mishacucicea/RedAlert/API/RedAlert.API/RedAlert.API/Content/img/beforecompresing/chooseaction.png

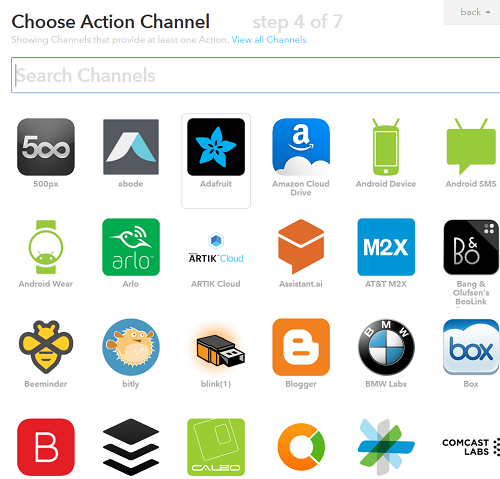
API/RedAlert.API/RedAlert.API/Content/img/beforecompresing/chooseaction.png
