mishacucicea/RedAlert/API/RedAlert.API/RedAlert.API/Content/img/beforecompresing/choosetriggerchanel.PNG

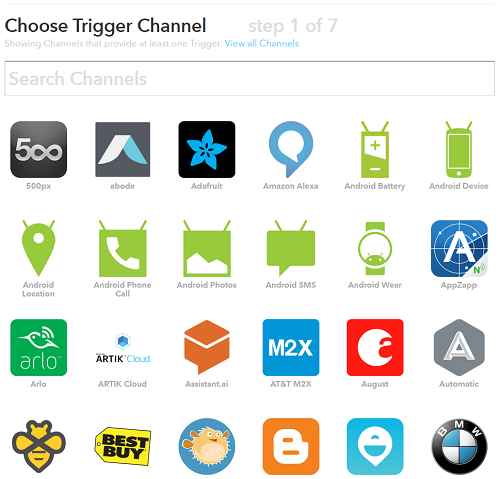
API/RedAlert.API/RedAlert.API/Content/img/beforecompresing/choosetriggerchanel.PNG
