mishacucicea/RedAlert/API/RedAlert.API/RedAlert.API/Content/img/beforecompresing/colorbubble.png

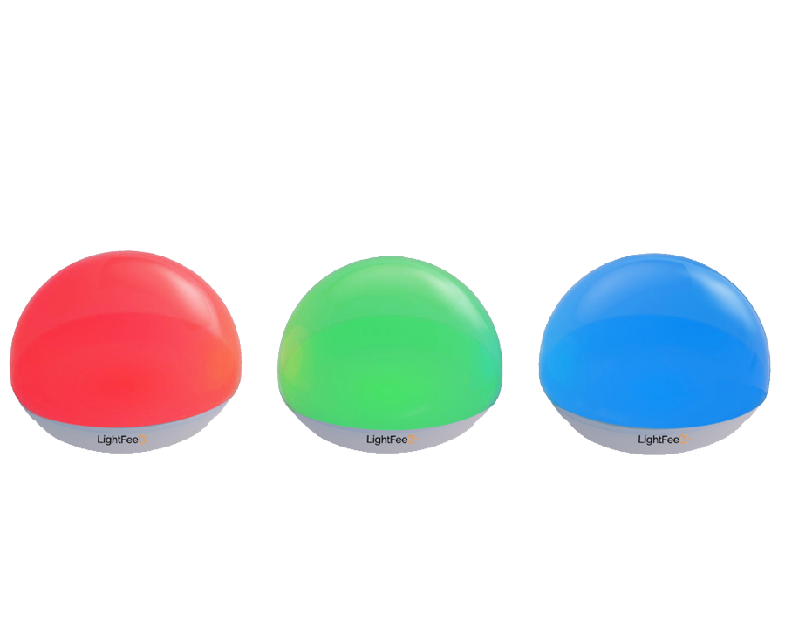
API/RedAlert.API/RedAlert.API/Content/img/beforecompresing/colorbubble.png
