mishacucicea/RedAlert/API/RedAlert.API/RedAlert.API/Content/img/beforecompresing/Colorbubbles.jpg

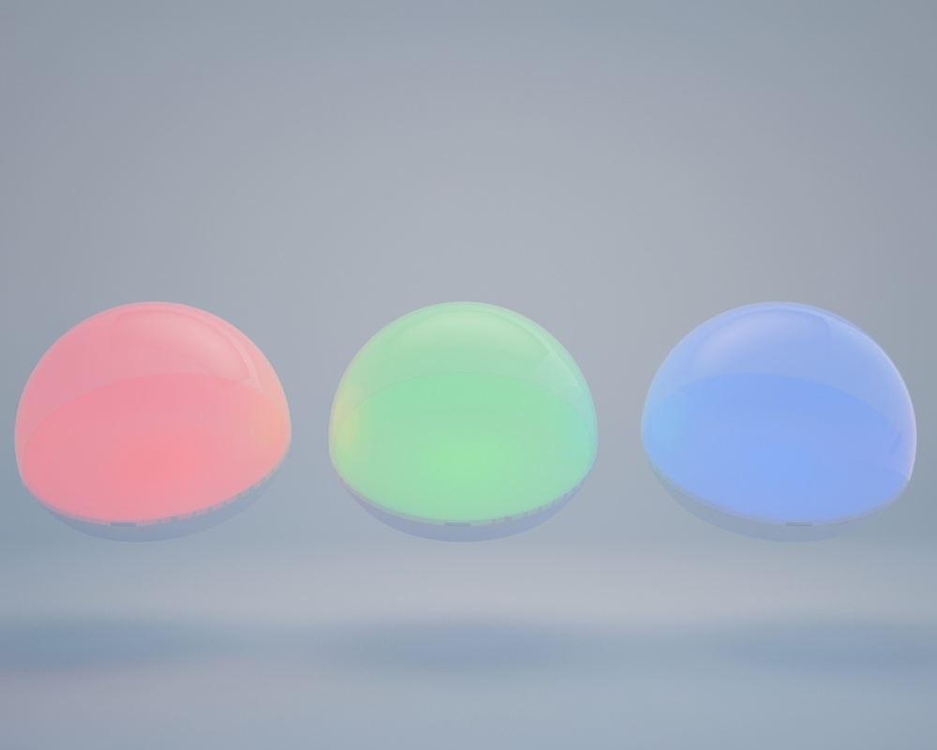
API/RedAlert.API/RedAlert.API/Content/img/beforecompresing/Colorbubbles.jpg
