mishacucicea/RedAlert/API/RedAlert.API/RedAlert.API/Content/img/beforecompresing/devicepsd.jpg

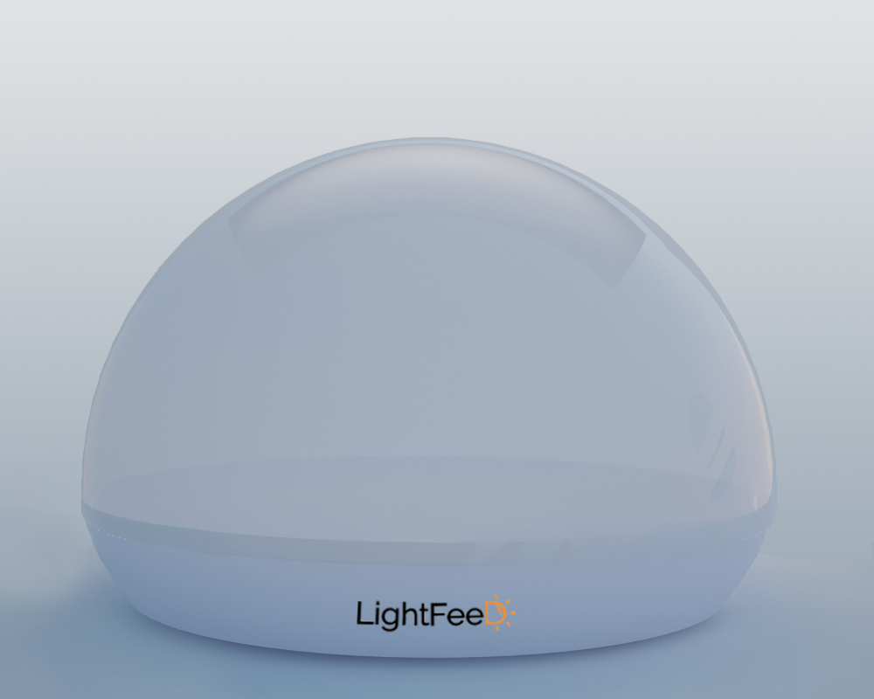
API/RedAlert.API/RedAlert.API/Content/img/beforecompresing/devicepsd.jpg
