mishacucicea/RedAlert/API/RedAlert.API/RedAlert.API/Content/img/beforecompresing/devicepsd.png

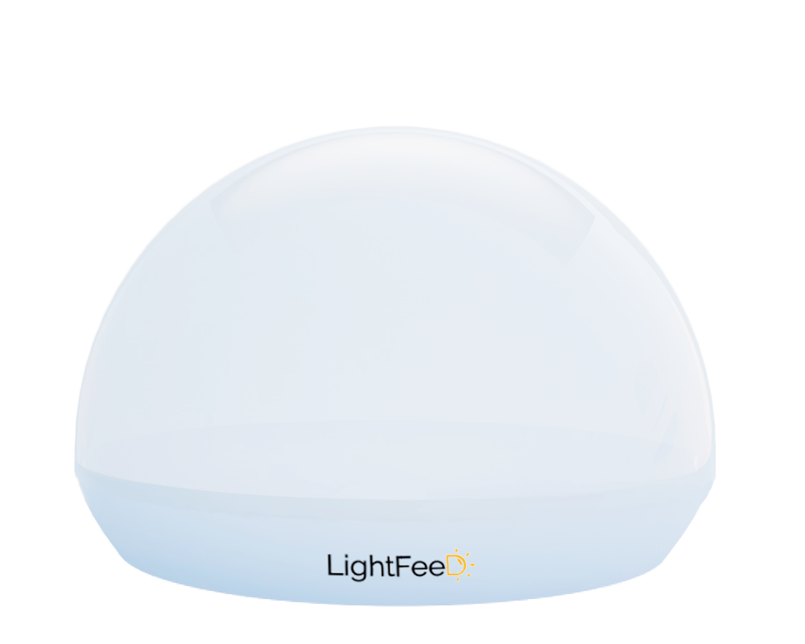
API/RedAlert.API/RedAlert.API/Content/img/beforecompresing/devicepsd.png
