mishacucicea/RedAlert/API/RedAlert.API/RedAlert.API/Content/img/beforecompresing/jenkins-solution.png

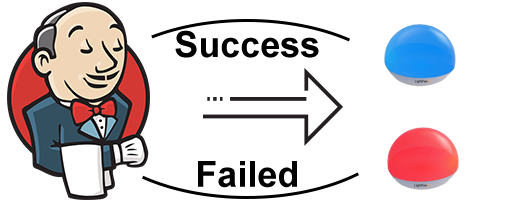
API/RedAlert.API/RedAlert.API/Content/img/beforecompresing/jenkins-solution.png
