mishacucicea/RedAlert/API/RedAlert.API/RedAlert.API/Content/img/beforecompresing/jenkins.jpg

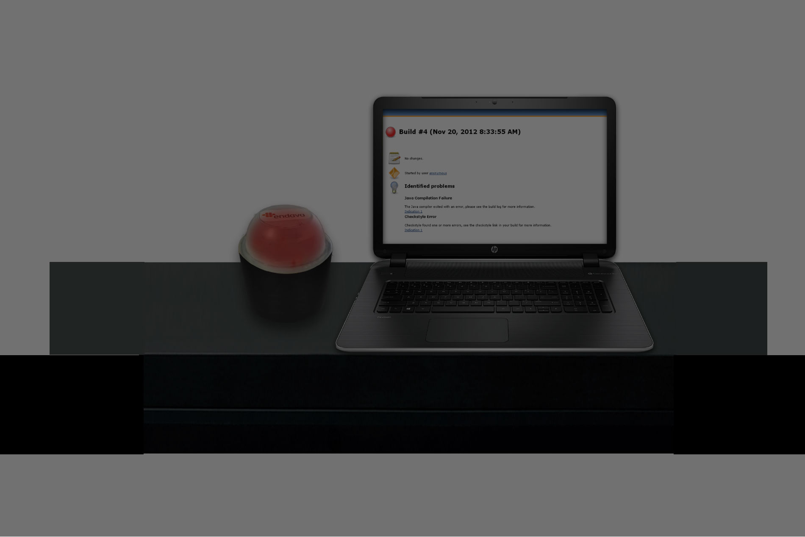
API/RedAlert.API/RedAlert.API/Content/img/beforecompresing/jenkins.jpg
