mishacucicea/RedAlert/API/RedAlert.API/RedAlert.API/Content/img/beforecompresing/scanqr.png

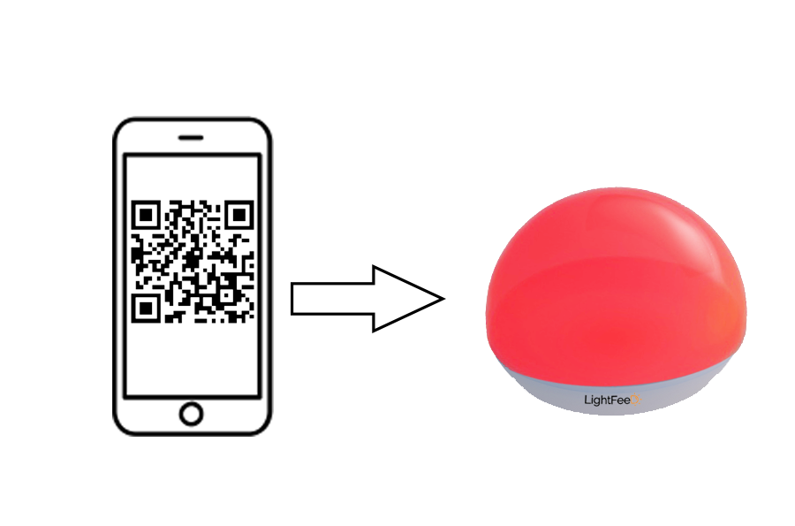
API/RedAlert.API/RedAlert.API/Content/img/beforecompresing/scanqr.png
