mishacucicea/RedAlert/API/RedAlert.API/RedAlert.API/Content/img/devicepsd.png

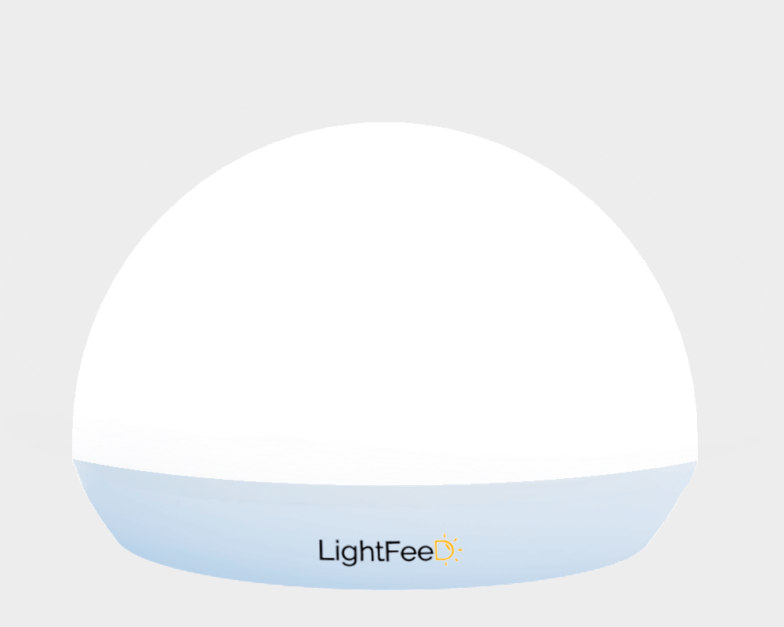
API/RedAlert.API/RedAlert.API/Content/img/devicepsd.png
