mishacucicea/RedAlert/API/RedAlert.API/RedAlert.API/Content/img/devicepsdxx.png

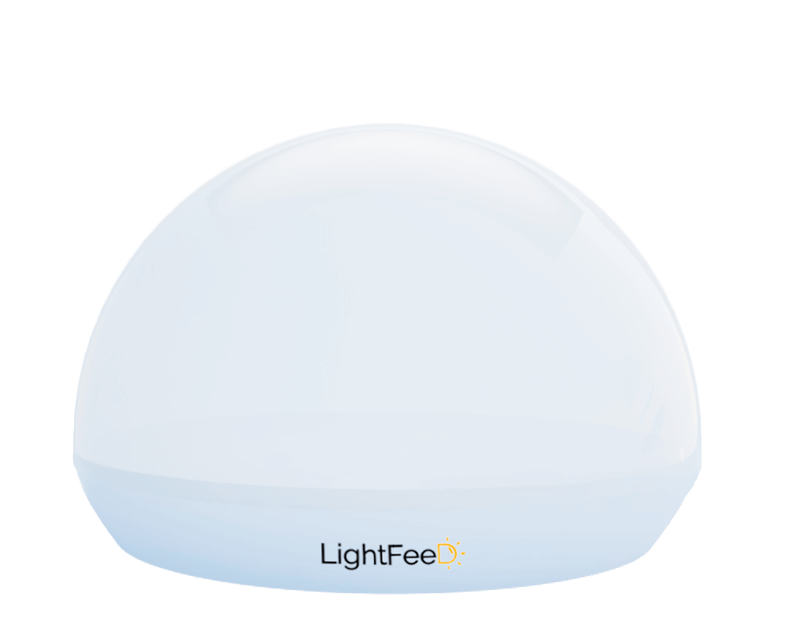
API/RedAlert.API/RedAlert.API/Content/img/devicepsdxx.png
