mishacucicea/RedAlert/API/RedAlert.API/RedAlert.API/Content/img/Frame50.gif

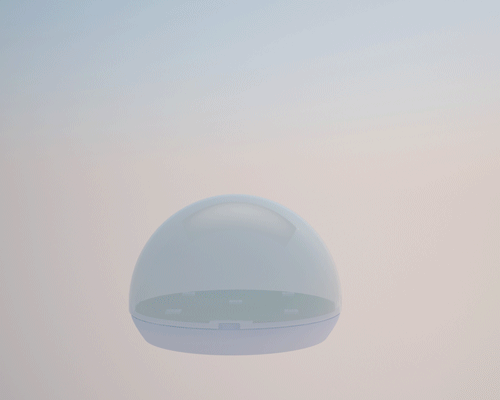
API/RedAlert.API/RedAlert.API/Content/img/Frame50.gif
