mishacucicea/RedAlert/API/RedAlert.API/RedAlert.API/Content/img/iftttlight.png

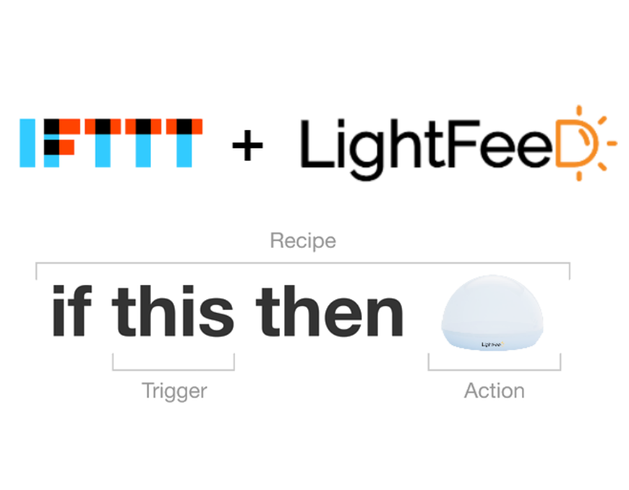
API/RedAlert.API/RedAlert.API/Content/img/iftttlight.png
