mishacucicea/RedAlert/API/RedAlert.API/RedAlert.API/Content/img/RGB_circle.png

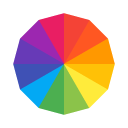
API/RedAlert.API/RedAlert.API/Content/img/RGB_circle.png
