mishacucicea/RedAlert/API/RedAlert.API/RedAlert.API/Content/img/team/1.jpg

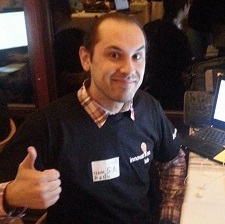
API/RedAlert.API/RedAlert.API/Content/img/team/1.jpg
