mishacucicea/RedAlert/API/RedAlert.API/RedAlert.API/Content/img/team/2.jpg

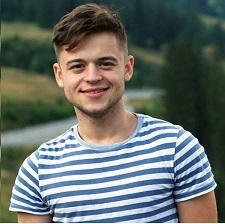
API/RedAlert.API/RedAlert.API/Content/img/team/2.jpg
