mishacucicea/RedAlert/API/RedAlert.API/RedAlert.API/Content/img/beforecompresing/maker.png

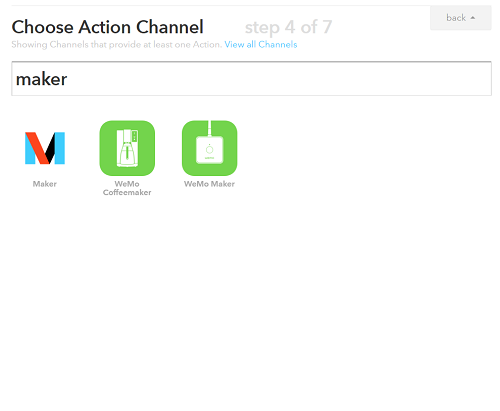
API/RedAlert.API/RedAlert.API/Content/img/beforecompresing/maker.png
