mishacucicea/RedAlert/API/RedAlert.API/RedAlert.API/Content/img/beforecompresing/makerurl.png

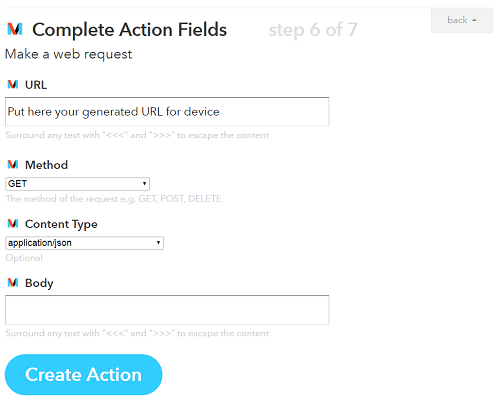
API/RedAlert.API/RedAlert.API/Content/img/beforecompresing/makerurl.png
